danjulio/Geiger-Counter/firmware/components/lvgl_drivers/lvgl_tft/disp_driver.h

/**
 * @file disp_driver.h
 */

#ifndef DISP_DRIVER_H
#define DISP_DRIVER_H

#ifdef __cplusplus
extern "C" {
#endif

/*********************
 *      INCLUDES
 *********************/
#include <stdbool.h>
#include "lvgl/lvgl.h"
#include "config.h"


/*********************
 *      DEFINES
 *********************/
 

/**********************
 *      TYPEDEFS
 **********************/
 

/**********************
 * GLOBAL PROTOTYPES
 **********************/
void disp_driver_init(bool init_spi);
void disp_driver_flush(lv_disp_drv_t * drv, const lv_area_t * area, lv_color_t * color_map);


/**********************
 *      MACROS
 **********************/

#ifdef __cplusplus
} /* extern "C" */
#endif

#endif /*DISP_DRIVER_H*/
