danjulio/Geiger-Counter/firmware/components/lvgl_drivers/lvgl_tft/disp_spi.h

/**
 * @file disp_spi.h
 *
 */

#ifndef DISP_SPI_H
#define DISP_SPI_H

#ifdef __cplusplus
extern "C" {
#endif

/*********************
 *      INCLUDES
 *********************/
#include <stdint.h>
#include <stdbool.h>
#include <driver/spi_master.h>
#include "lv_conf.h"
#include "config.h"



/*********************
 *      DEFINES
 *********************/
 
// SPI Bus when using disp_spi_init()
 #define DISP_SPI_HOST CONFIG_LCD_SPI_HOST

// Buffer size - sets maximum update region (and can use a lot of memory!)
#define DISP_BUF_SIZE CONFIG_LVGL_DISP_BUF_SIZE
 
// Display-specific GPIO
#define DISP_SPI_MOSI CONFIG_LCD_MOSI_IO
#define DISP_SPI_CLK  CONFIG_LCD_SCK_IO
#define DISP_SPI_CS   CONFIG_LCD_CSN_IO

// Display SPI frequency
#define DISP_SPI_HZ   CONFIG_LCD_SPI_FREQ_HZ

#define DISP_SPI_MODE    (2)


/**********************
 *      TYPEDEFS
 **********************/

/**********************
 * GLOBAL PROTOTYPES
 **********************/
void disp_spi_init(void);
void disp_spi_add_device(spi_host_device_t host);
void disp_spi_send_data(uint8_t * data, uint16_t length);
void disp_spi_send_colors(uint8_t * data, uint16_t length);
bool disp_spi_is_busy(void);

/**********************
 *      MACROS
 **********************/


#ifdef __cplusplus
} /* extern "C" */
#endif

#endif /*DISP_SPI_H*/
